makserge/LedMatrixSensorNode/schematics/LedMatrixSensorNode/LedMatrixSensorNode.kicad_sch

## KiCad design schematics/LedMatrixSensorNode/LedMatrixSensorNode.kicad_sch (2026-08-01, an earlier design)

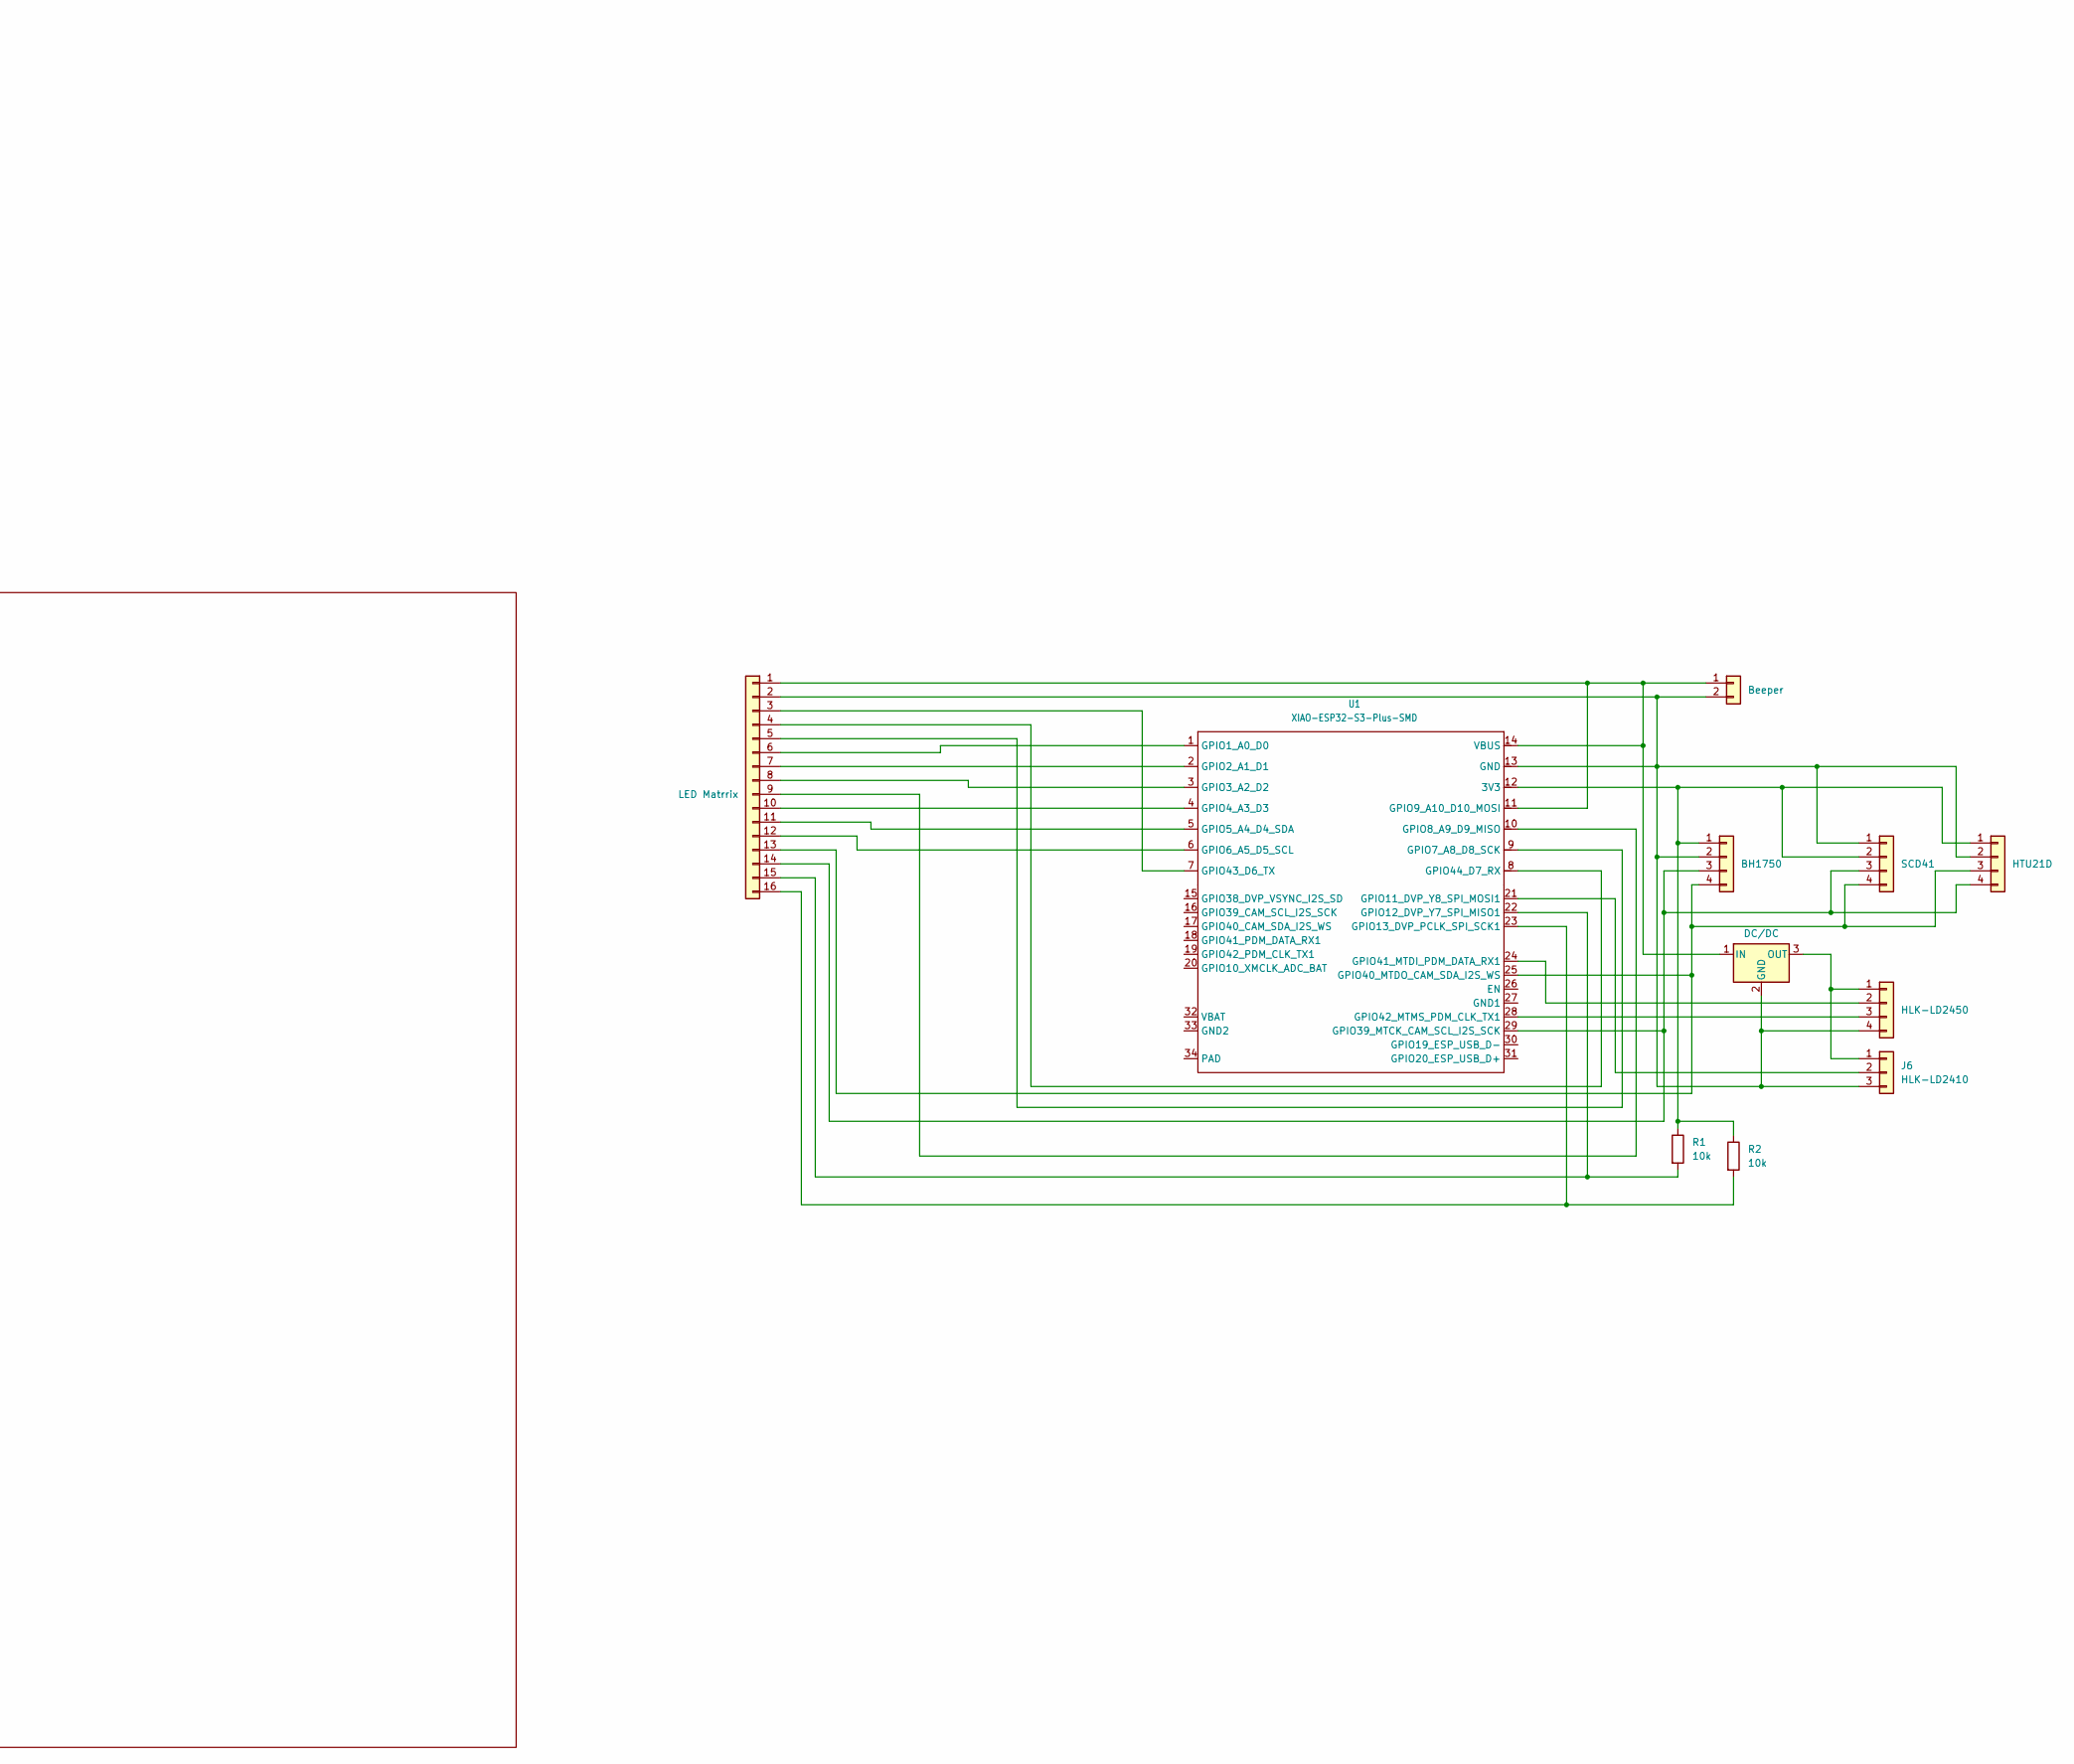
[picture p3: schematic LedMatrixSensorNode.kicad_sch, part in row 1, column 2]

Parts:
J2: BH1750
J3: SCD41
J4: HTU21D
J5: HLK-LD2450
J6: HLK-LD2410
J7: Beeper
J9: LED Matrrix
R1, R2: 10k
U1: XIAO-ESP32-S3-Plus-SMD
U2: DC/DC

Connections:
unnamed: J2.1, J3.2, J4.1, R1.1, R2.1, U1.12 (3V3)
unnamed: J2.2, J3.1, J4.2, J5.4, J6.3, J7.2, J9.2, U1.13 (GND), U2.2 (GND)
unnamed: J2.3, J3.3, J4.4, J9.14, U1.29 (GPIO39_MTCK_CAM_SCL_I2S_SCK)
unnamed: J2.4, J3.4, J4.3, J9.13, U1.25 (GPIO40_MTDO_CAM_SDA_I2S_WS)
unnamed: J5.1, J6.1, U2.3 (OUT)
unnamed: J5.2, U1.24 (GPIO41_MTDI_PDM_DATA_RX1)
unnamed: J5.3, U1.28 (GPIO42_MTMS_PDM_CLK_TX1)
unnamed: J6.2, U1.21 (GPIO11_DVP_Y8_SPI_MOSI1)
unnamed: J7.1, J9.1, U1.11 (GPIO9_A10_D10_MOSI), U1.14 (VBUS), U2.1 (IN)
unnamed: J9.3, U1.7 (GPIO43_D6_TX)
unnamed: J9.4, U1.8 (GPIO44_D7_RX)
unnamed: J9.5, U1.9 (GPIO7_A8_D8_SCK)
unnamed: J9.6, U1.1 (GPIO1_A0_D0)
unnamed: J9.7, U1.2 (GPIO2_A1_D1)
unnamed: J9.8, U1.3 (GPIO3_A2_D2)
unnamed: J9.9, U1.10 (GPIO8_A9_D9_MISO)
unnamed: J9.10, U1.4 (GPIO4_A3_D3)
unnamed: J9.11, U1.5 (GPIO5_A4_D4_SDA)
unnamed: J9.12, U1.6 (GPIO6_A5_D5_SCL)
unnamed: J9.15, R1.2, U1.22 (GPIO12_DVP_Y7_SPI_MISO1)
unnamed: J9.16, R2.2, U1.23 (GPIO13_DVP_PCLK_SPI_SCK1)
