makserge/LedMatrixSensorNode/schematics/LedMatrixSensorNode/led_matrix_driver.kicad_sch

## KiCad design schematics/LedMatrixSensorNode/led_matrix_driver.kicad_sch (2026-05-25, an earlier design)

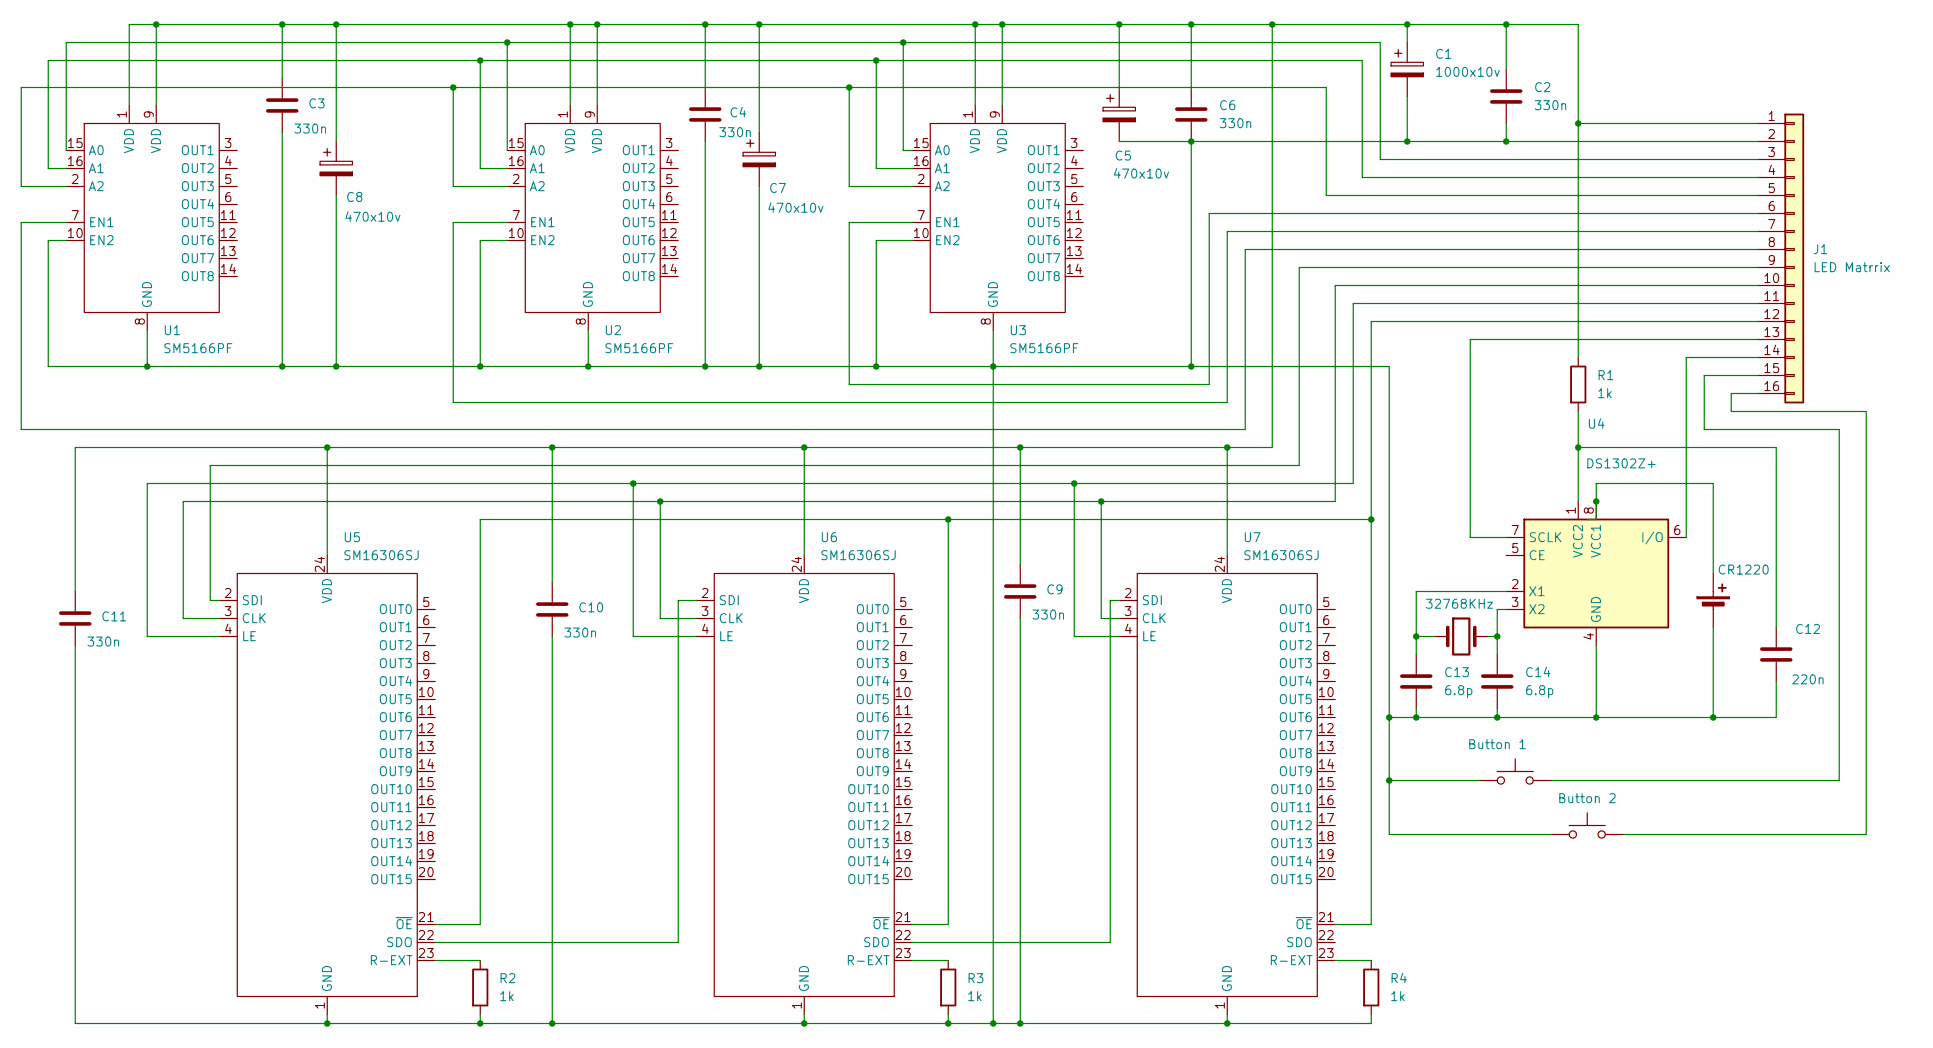
[picture p4: schematic led_matrix_driver.kicad_sch]

Parts:
BT1: CR1220
C1: 1000x10v
C2, C3, C4, C6, C9, C10, C11: 330n
C5, C7, C8: 470x10v
C12: 220n
C13, C14: 6.8p
J1: LED Matrrix
R1, R2, R3, R4: 1k
SW1: Button 1
SW2: Button 2
U1, U2, U3: SM5166PF
U4: DS1302Z+; SOIC-8_3.9x4.9mm_P1.27mm
U5, U6, U7: SM16306SJ; QSOP-24_3.9x8.7mm_P0.635mm
Y1: 32768KHz

Connections:
unnamed: BT1.1 (+), U4.8 (VCC1)
unnamed: BT1.2 (-), C1.2, C2.2, C3.2, C4.2, C5.2, C6.2, C7.2, C8.2, C9.2, C10.2, C11.2, C12.2, C13.2, C14.2, J1.2, R2.2, R3.2, R4.2, SW1.1, SW2.1, U1.8 (GND), U1.10 (EN2), U2.8 (GND), U2.10 (EN2), U3.8 (GND), U3.10 (EN2), U4.4 (GND), U5.1 (GND), U6.1 (GND), U7.1 (GND)
unnamed: C1.1, C2.1, C3.1, C4.1, C5.1, C6.1, C7.1, C8.1, C9.1, C10.1, C11.1, J1.1, R1.1, U1.1 (VDD), U1.9 (VDD), U2.1 (VDD), U2.9 (VDD), U3.1 (VDD), U3.9 (VDD), U5.24 (VDD), U6.24 (VDD), U7.24 (VDD)
unnamed: C12.1, R1.2, U4.1 (VCC2)
unnamed: C13.1, U4.2 (X1), Y1.1
unnamed: C14.1, U4.3 (X2), Y1.2
unnamed: J1.3, U1.15 (A0), U2.15 (A0), U3.15 (A0)
unnamed: J1.4, U1.16 (A1), U2.16 (A1), U3.16 (A1)
unnamed: J1.5, U1.2 (A2), U2.2 (A2), U3.2 (A2)
unnamed: J1.6, U3.7 (EN1)
unnamed: J1.7, U2.7 (EN1)
unnamed: J1.8, U1.7 (EN1)
unnamed: J1.9, U5.2 (SDI)
unnamed: J1.10, U5.3 (CLK), U6.3 (CLK), U7.3 (CLK)
unnamed: J1.11, U5.4 (LE), U6.4 (LE), U7.4 (LE)
unnamed: J1.12, U5.21 (~OE), U6.21 (~OE), U7.21 (~OE)
unnamed: J1.13, U4.7 (SCLK)
unnamed: J1.14, U4.6 (I/O)
unnamed: J1.15, SW1.2
unnamed: J1.16, SW2.2
unnamed: R2.1, U5.23 (R-EXT)
unnamed: R3.1, U6.23 (R-EXT)
unnamed: R4.1, U7.23 (R-EXT)
unnamed: U5.22 (SDO), U6.2 (SDI)
unnamed: U6.22 (SDO), U7.2 (SDI)
