makserge/LedMatrixSensorNode/include/light_sensor.h

#ifndef LIGHT_SENSOR_H
#define LIGHT_SENSOR_H

#include <Arduino.h>
#include <BH1750.h>
#include <math.h>
#include "constants.h"
#include "display_manager.h"
#include "i2c_mutex.h"
#include "led_matrix.h"
#include "task_registry.h"

class LightSensor {
public:
    void begin();
    void update();
    float getCurrentLux() const { return _currentLux; }
    uint8_t getMatrixBrightness() const { return _matrixBrightness; }

private:
    BH1750 _lightMeter;
    float _currentLux = 0.0f;
    uint8_t _matrixBrightness = 32;
};

extern LightSensor lightSensor;

void initLightSensorTask();

#endif
