makserge/LedMatrixSensorNode/include/ntp_clock.h

#ifndef NTP_CLOCK_H
#define NTP_CLOCK_H

#include <freertos/FreeRTOS.h>
#include <freertos/queue.h>
#include <Arduino.h>
#include "time.h"
#include "constants.h"
#include "task_registry.h"

struct ClockMessage {
    uint16_t text[6];
    int startX;
    bool synced;
};

class NtpClock {
public:
    void begin();
    void update(bool showColon);
};

extern QueueHandle_t clockQueue;

void initNtpClockTask();

#endif
