makserge/LedMatrixSensorNode/include/secrets.example.h

#ifndef SECRETS_H
#define SECRETS_H
 
static const char* const MQTT_HOST = "127.0.0.1";
static const char* const MQTT_USER = "";
static const char* const MQTT_PASS = "";
 
static const char* const AUDIO_STREAM_URL = "http://127.0.0.1:8000/stream.wav";
static const char* const WIFI_BACKUP_SSID = "";
static const char* const WIFI_BACKUP_PASS = "";
 
#endif
 
